turmandreams/pajitaraptor2/images/01.jpg

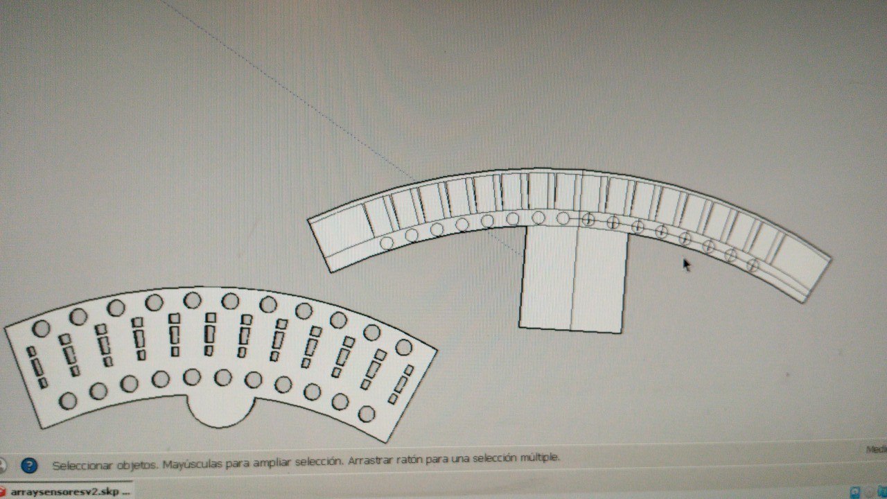
images/01.jpg
