turmandreams/pajitaraptor2/images/02.jpg

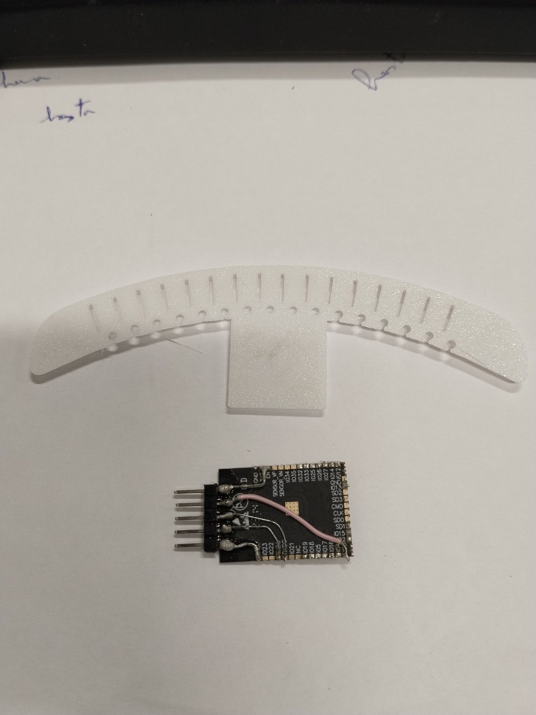
images/02.jpg
