turmandreams/pajitaraptor2/images/03.jpg

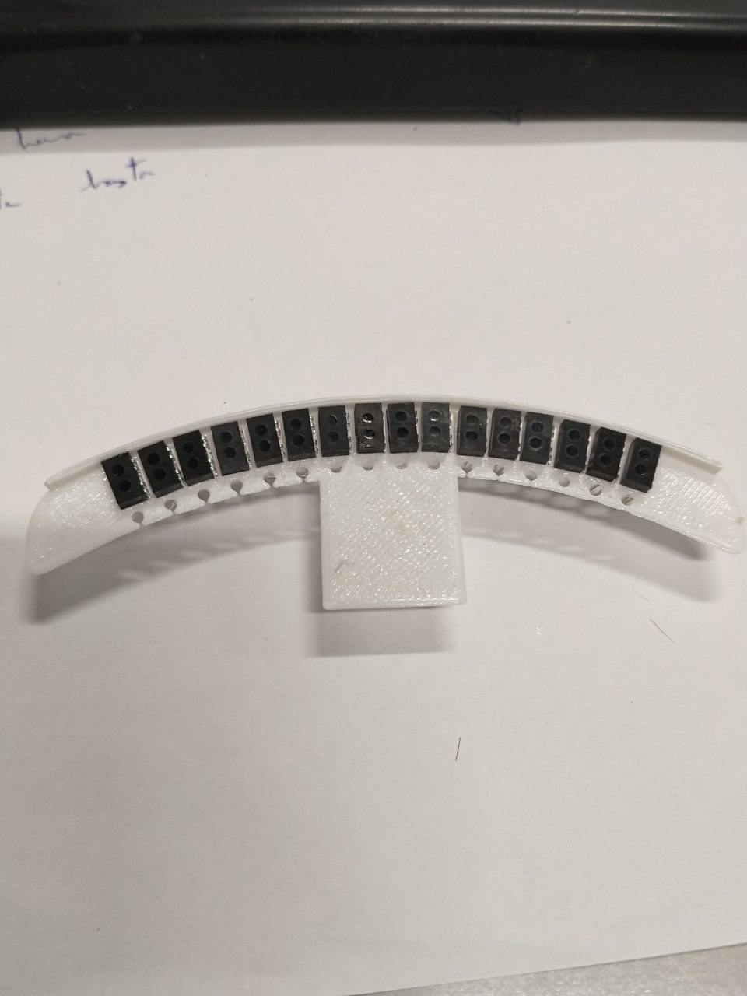
images/03.jpg
