turmandreams/pajitaraptor2/images/04.jpg

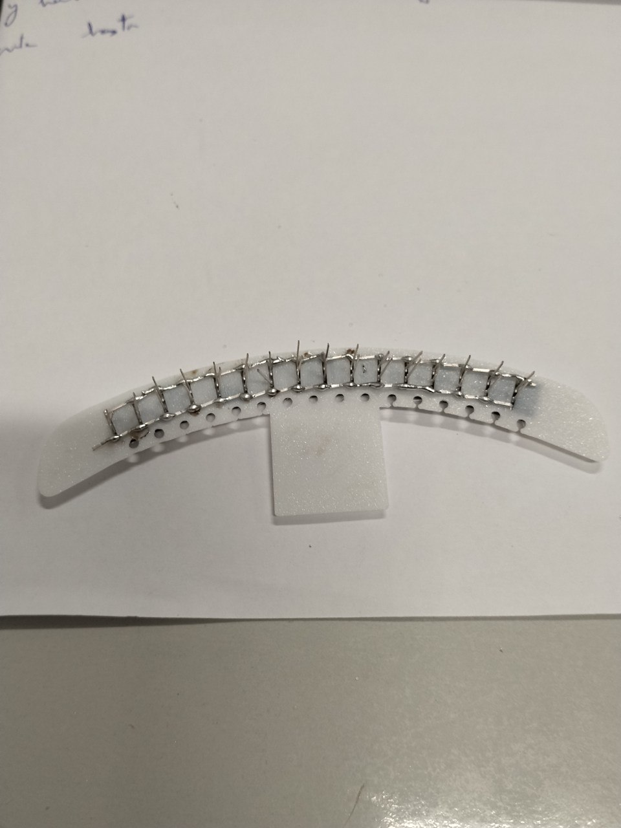
images/04.jpg
