turmandreams/pajitaraptor2/images/05.jpg

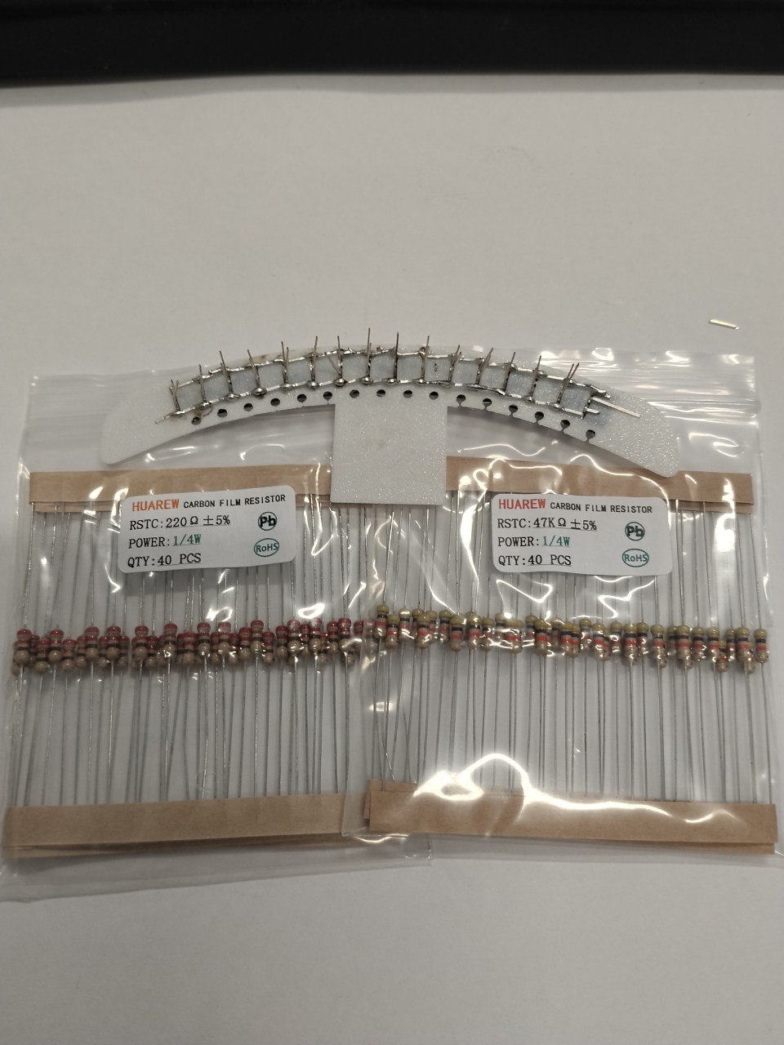
images/05.jpg
