turmandreams/pajitaraptor2/images/07.jpg

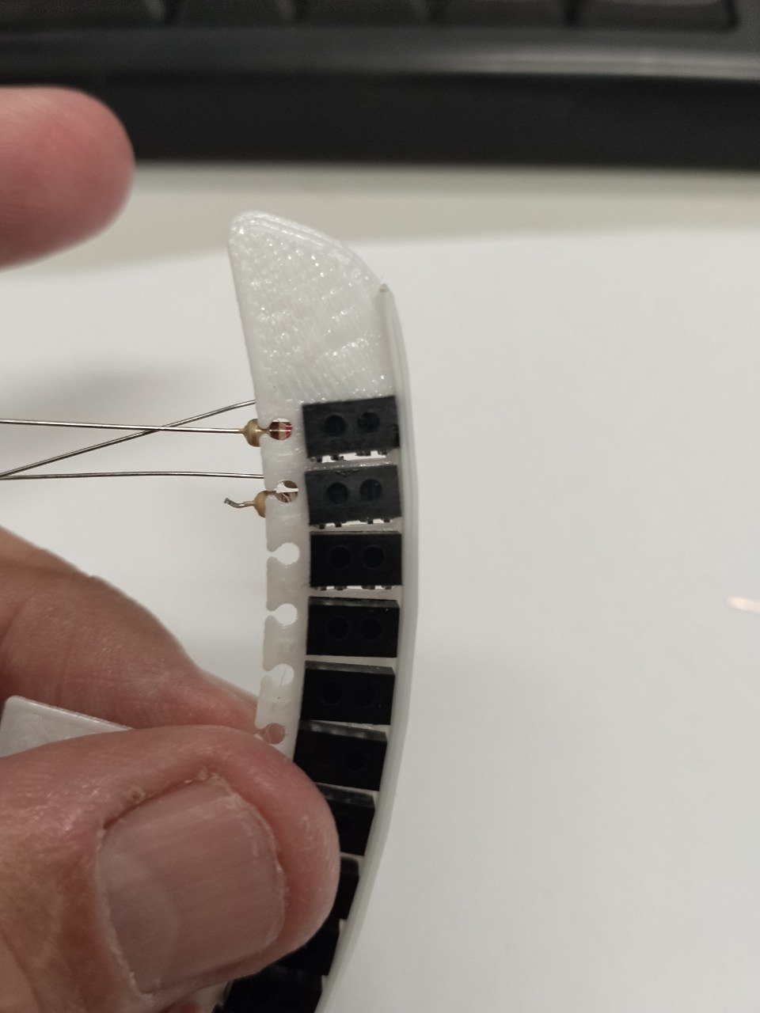
images/07.jpg
