turmandreams/pajitaraptor2/images/08.jpg

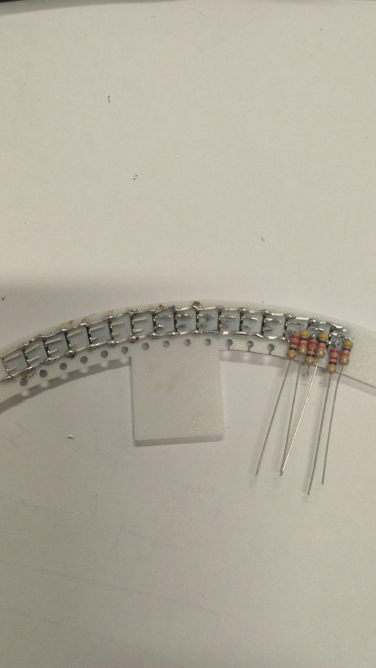
images/08.jpg
