turmandreams/pajitaraptor2/images/09.jpg

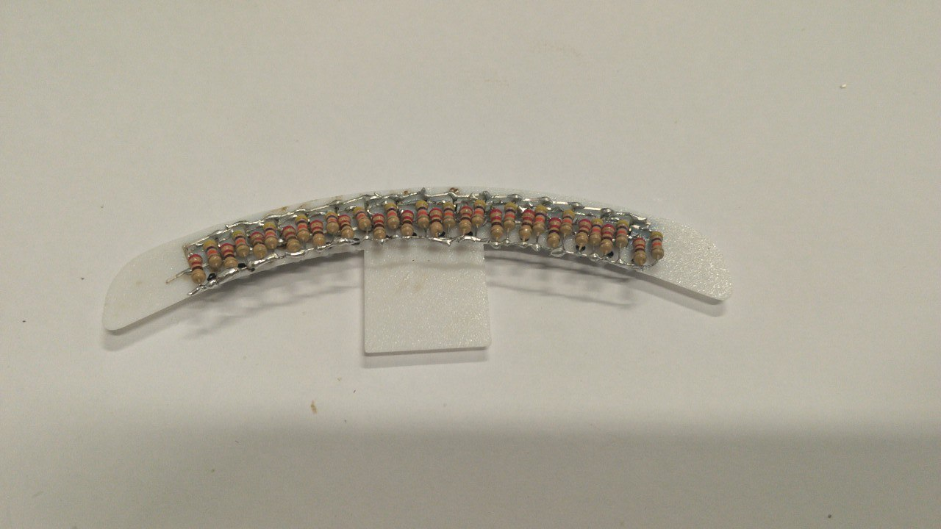
images/09.jpg
