turmandreams/pajitaraptor2/images/10.jpg

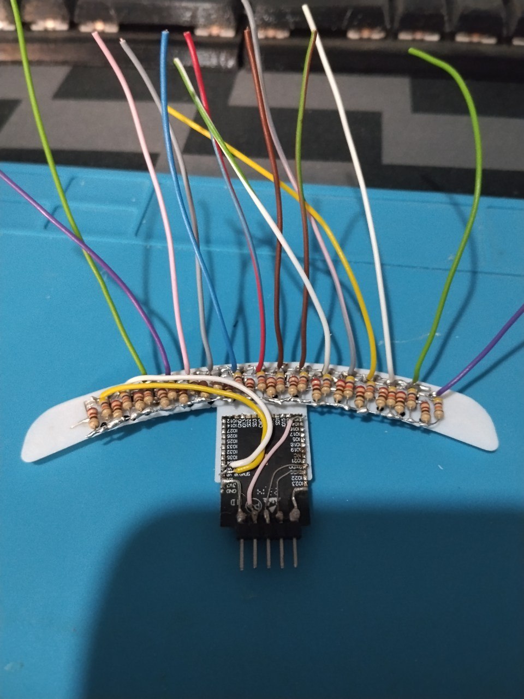
images/10.jpg
