turmandreams/pajitaraptor2/images/11.jpg

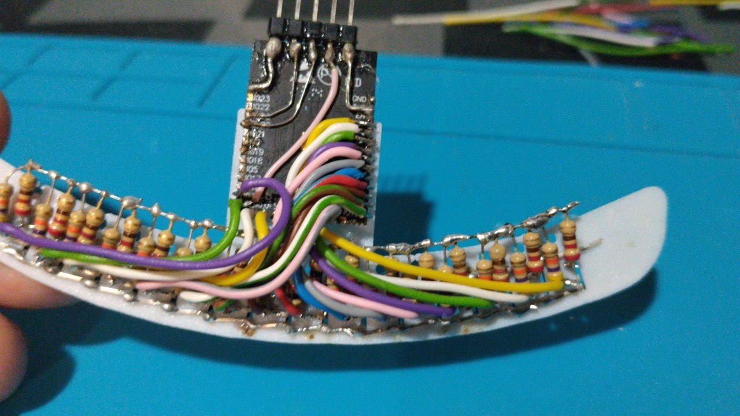
images/11.jpg
