turmandreams/pajitaraptor2/images/12.jpg

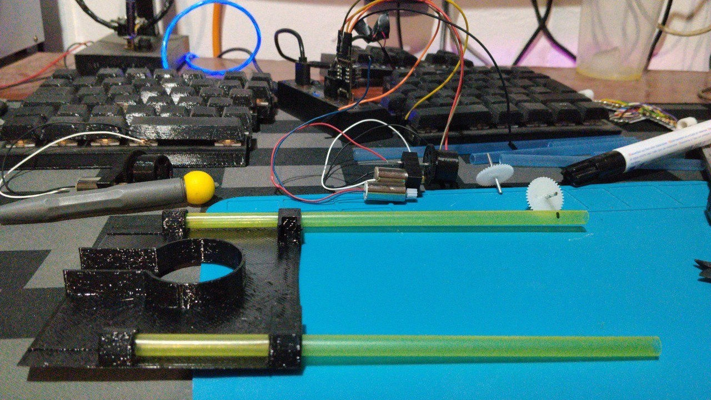
images/12.jpg
