turmandreams/pajitaraptor2/images/13.jpg

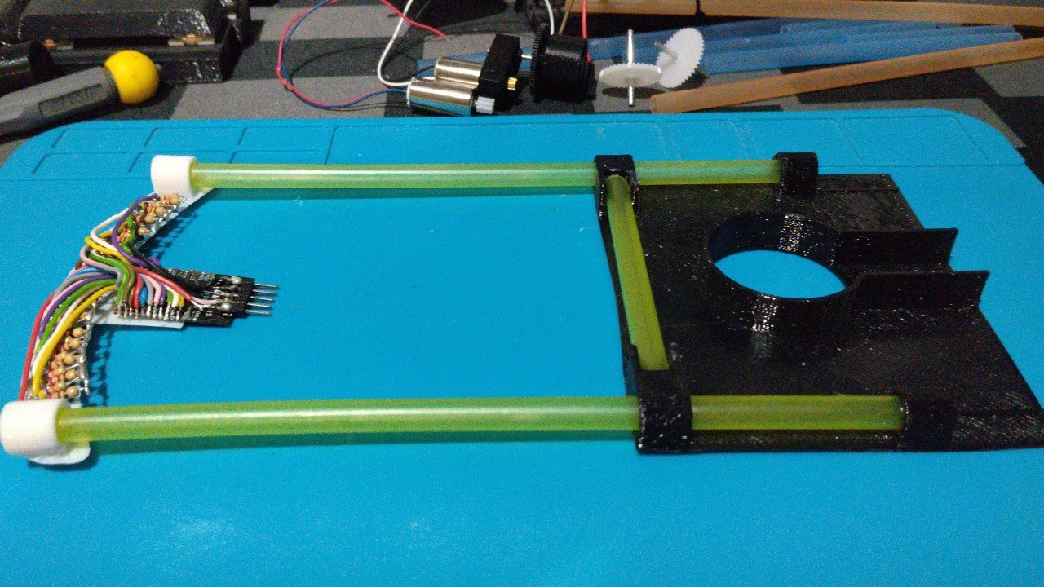
images/13.jpg
