turmandreams/pajitaraptor2/images/14.jpg

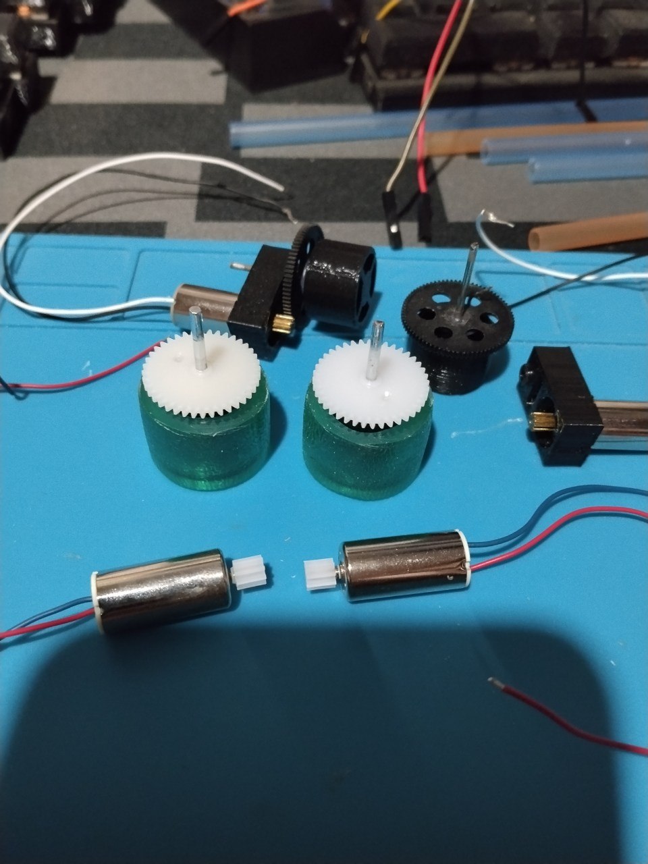
images/14.jpg
