turmandreams/pajitaraptor2/images/15.jpg

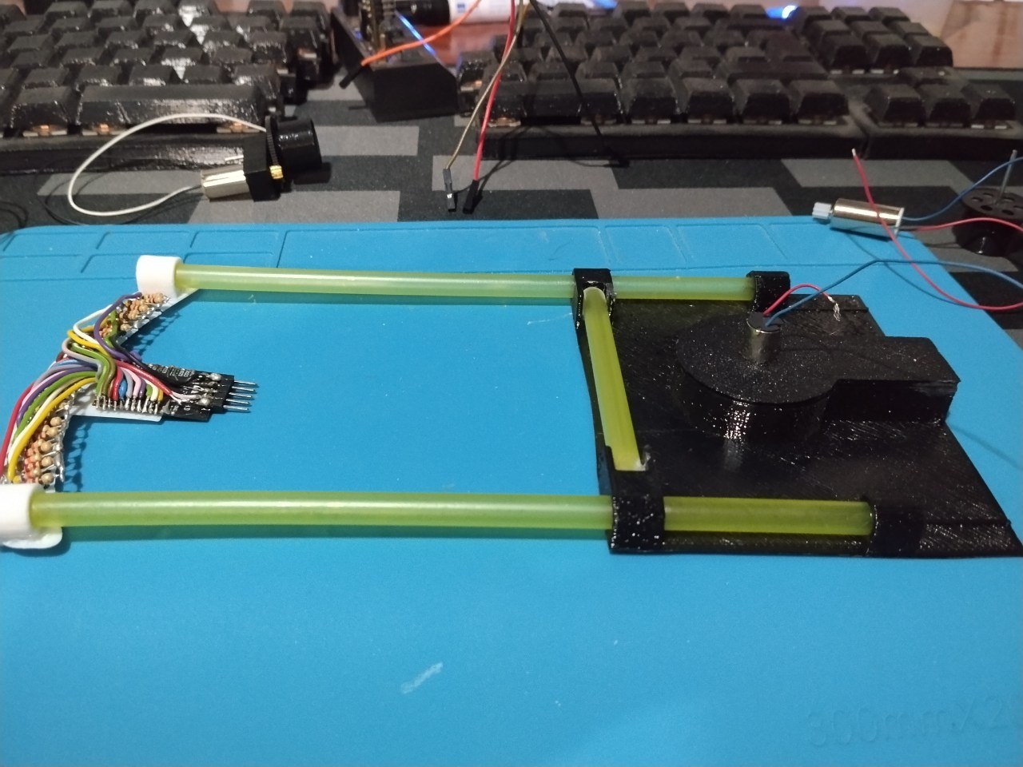
images/15.jpg
