turmandreams/pajitaraptor2/images/16.jpg

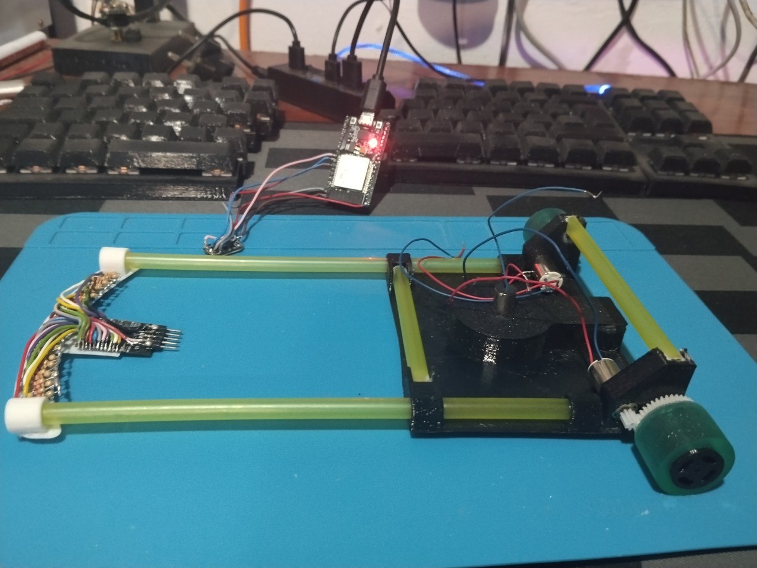
images/16.jpg
