turmandreams/pajitaraptor2/images/17.jpg

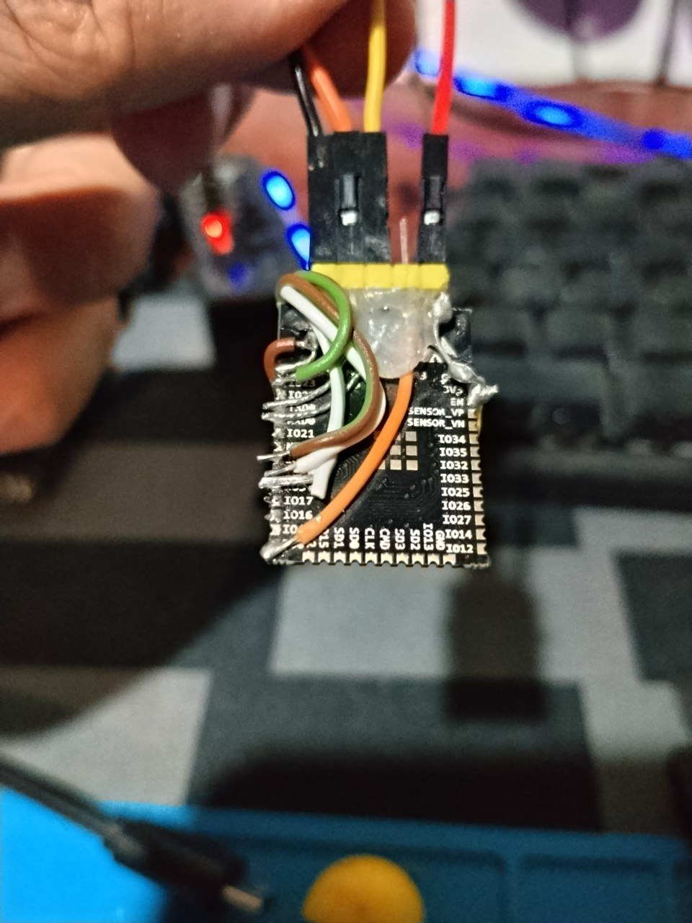
images/17.jpg
