turmandreams/pajitaraptor2/images/18.jpg

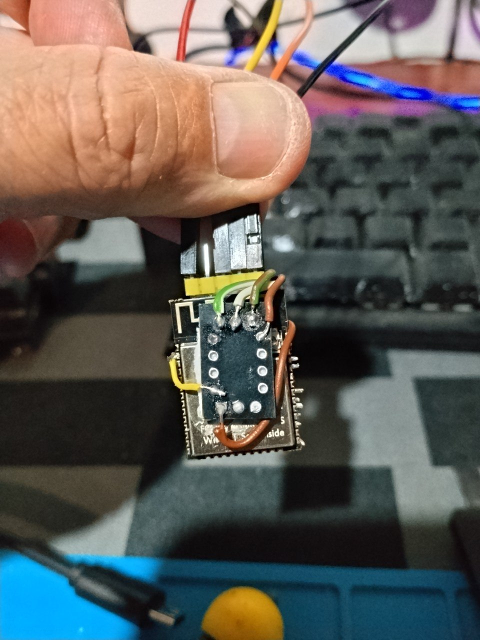
images/18.jpg
