turmandreams/pajitaraptor2/images/19.jpg

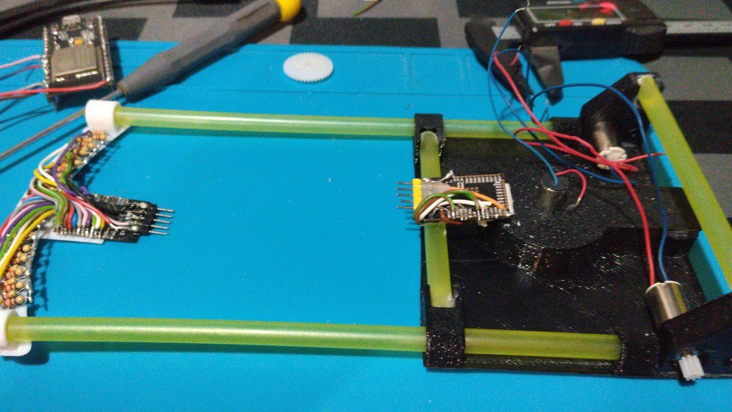
images/19.jpg
