turmandreams/pajitaraptor2/images/20.jpg

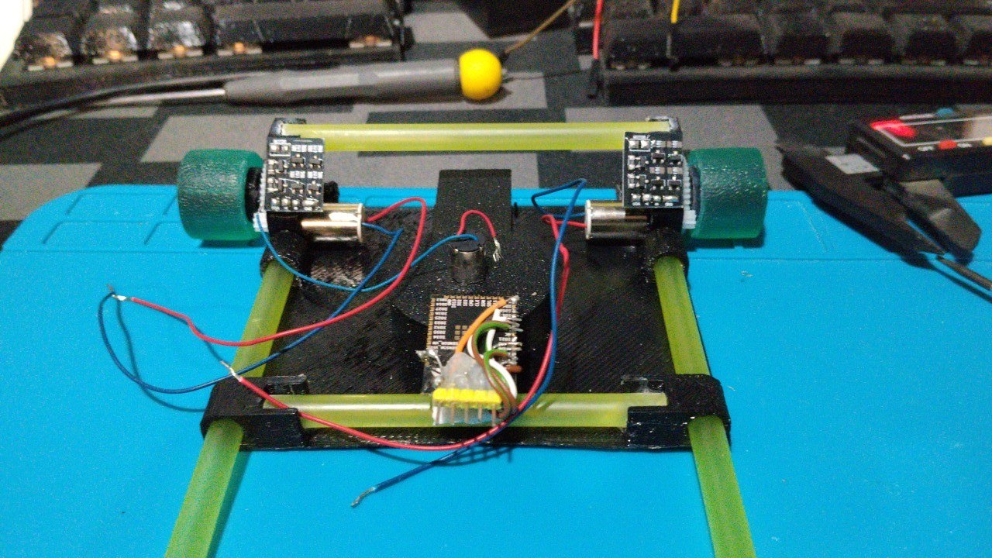
images/20.jpg
