turmandreams/pajitaraptor2/images/21.jpg

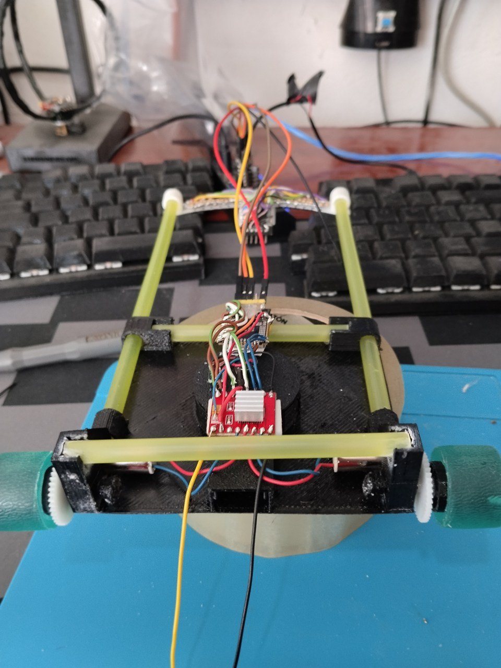
images/21.jpg
