turmandreams/pajitaraptor2/images/22.jpg

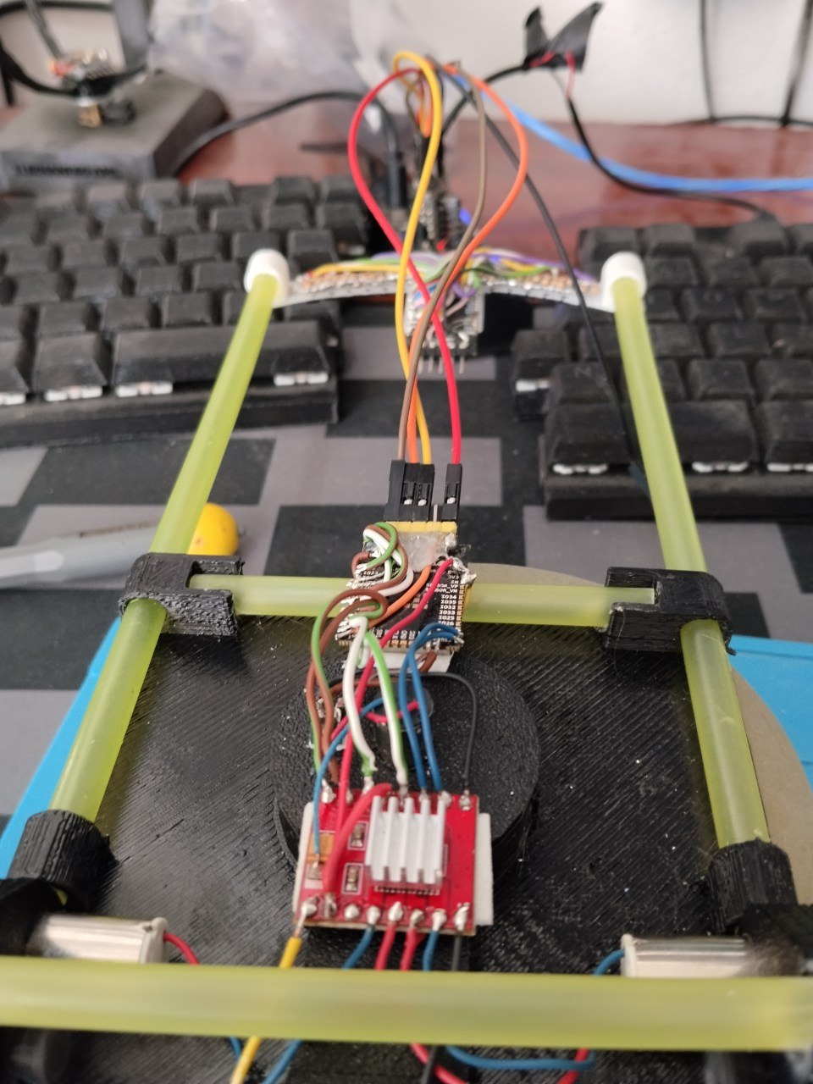
images/22.jpg
