turmandreams/pajitaraptor2/images/23.jpg

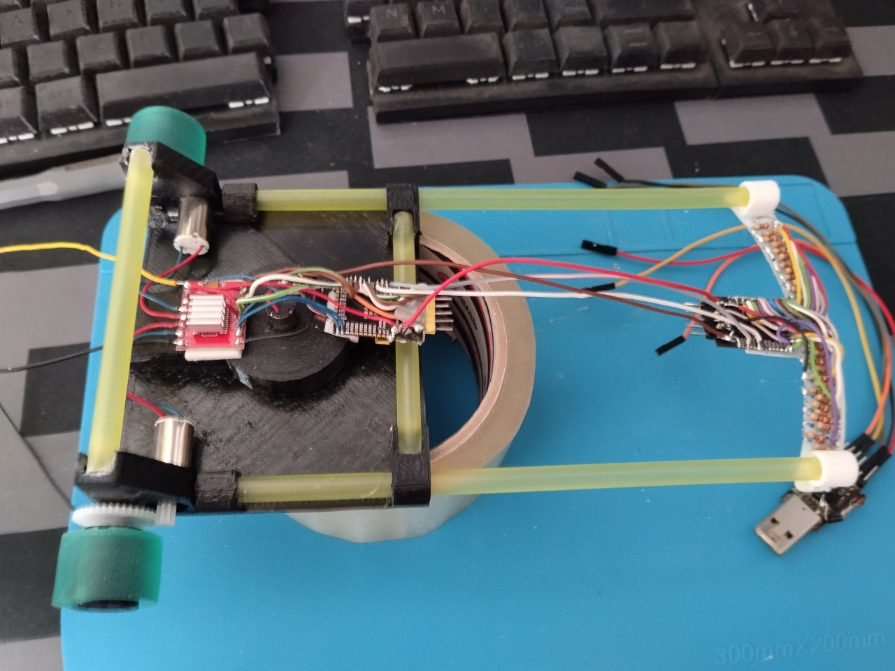
images/23.jpg
