turmandreams/pajitaraptor2/images/24.jpg

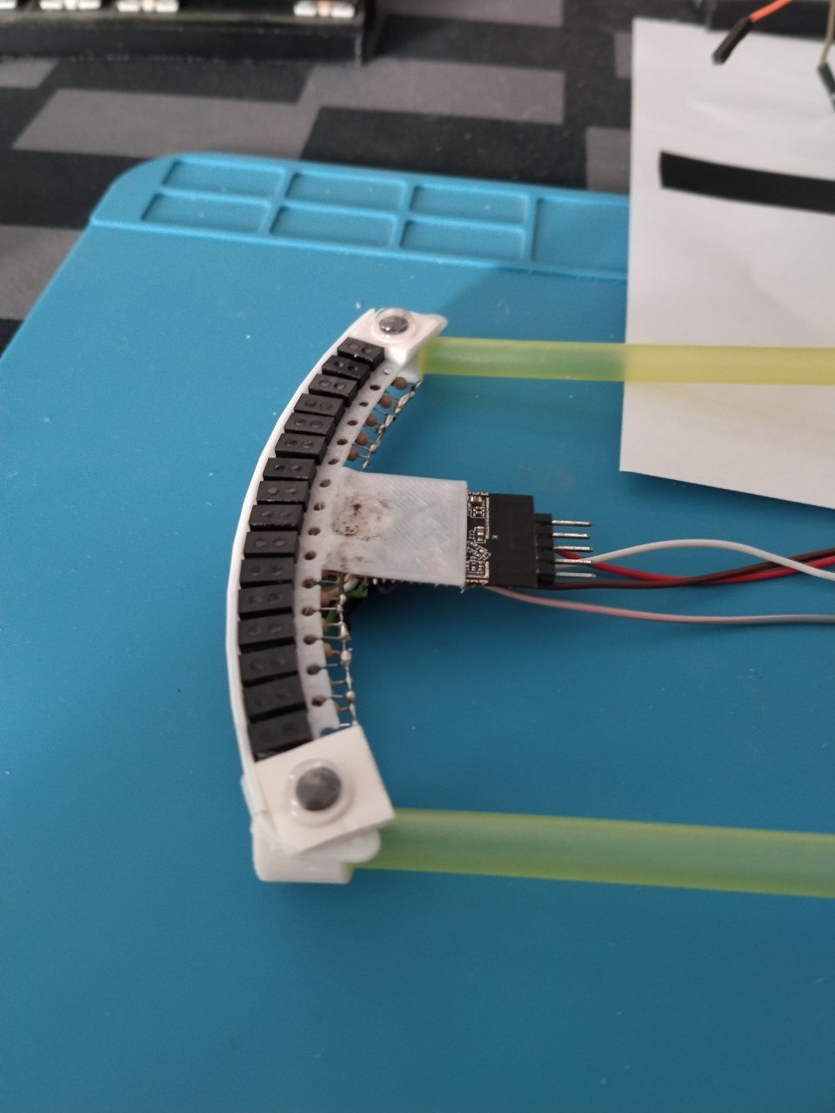
images/24.jpg
