turmandreams/pajitaraptor2/images/25.jpg

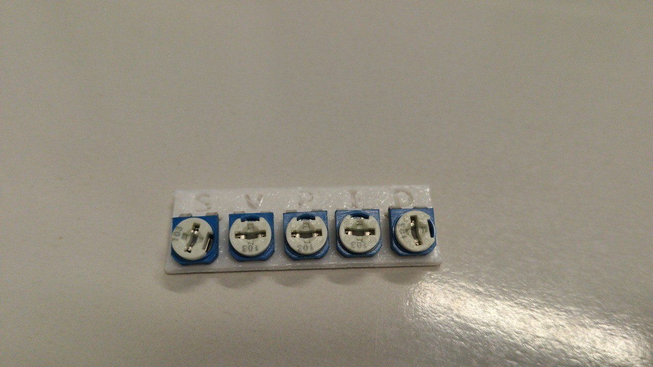
images/25.jpg
