turmandreams/pajitaraptor2/images/26.jpg

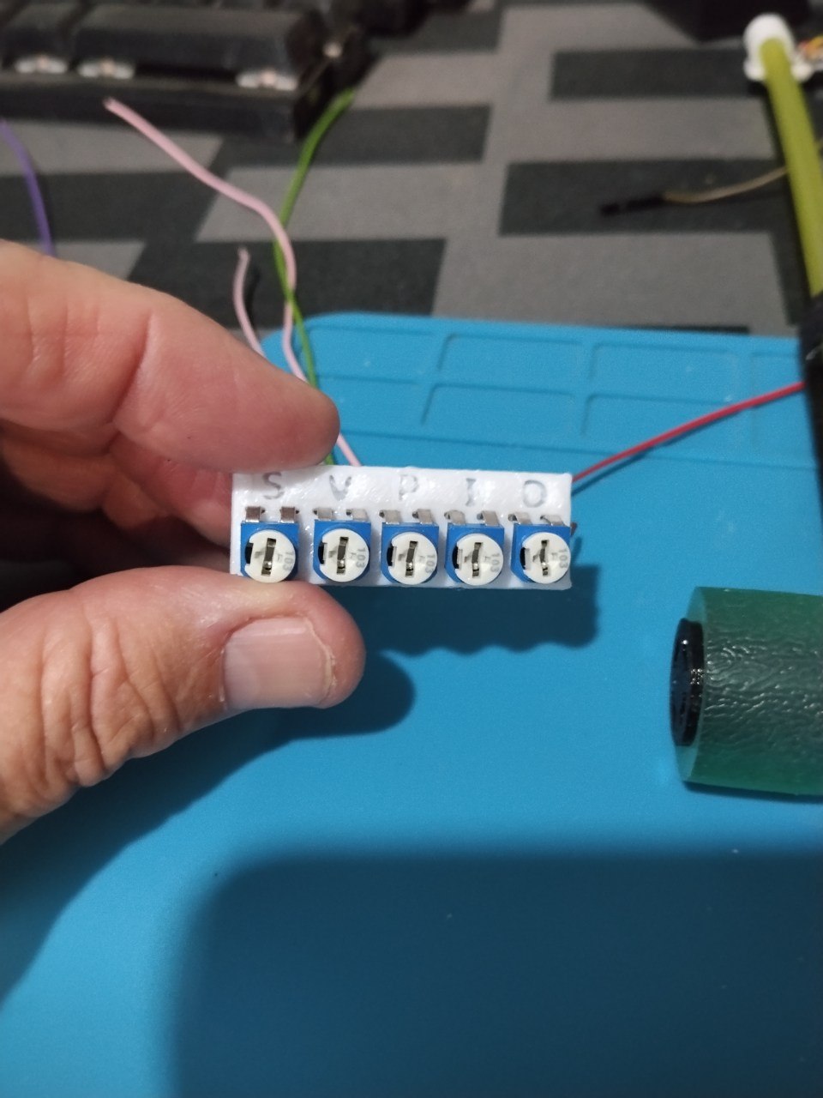
images/26.jpg
