turmandreams/pajitaraptor2/images/27.jpg

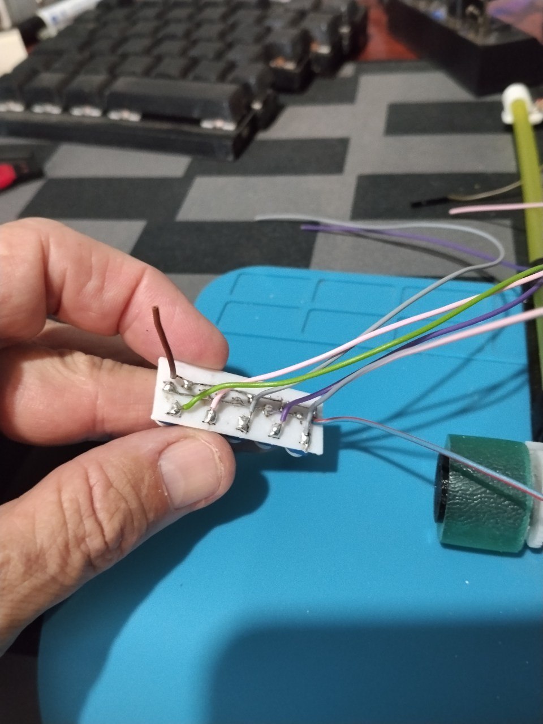
images/27.jpg
