turmandreams/pajitaraptor2/images/28.jpg

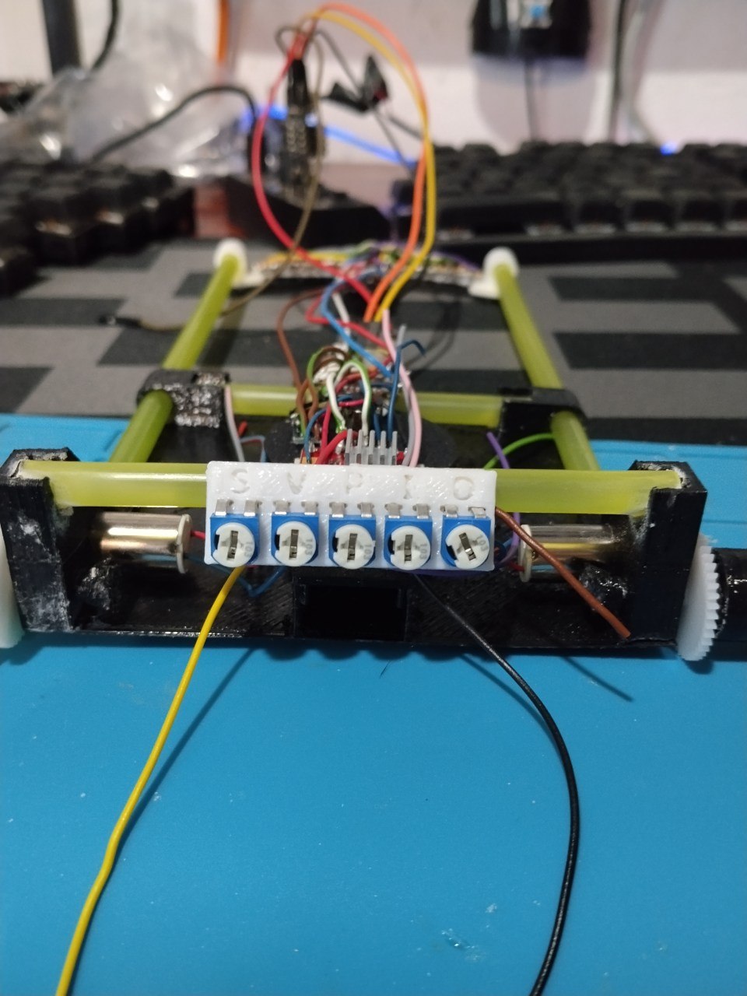
images/28.jpg
