turmandreams/pajitaraptor2/images/29.jpg

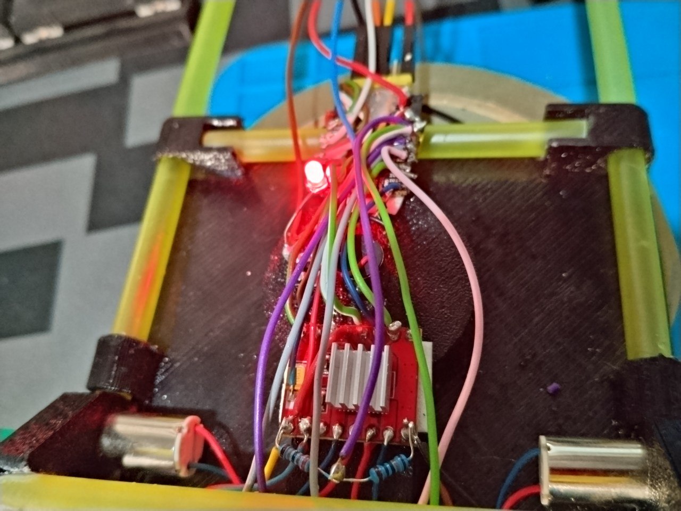
images/29.jpg
