turmandreams/pajitaraptor2/images/30.jpg

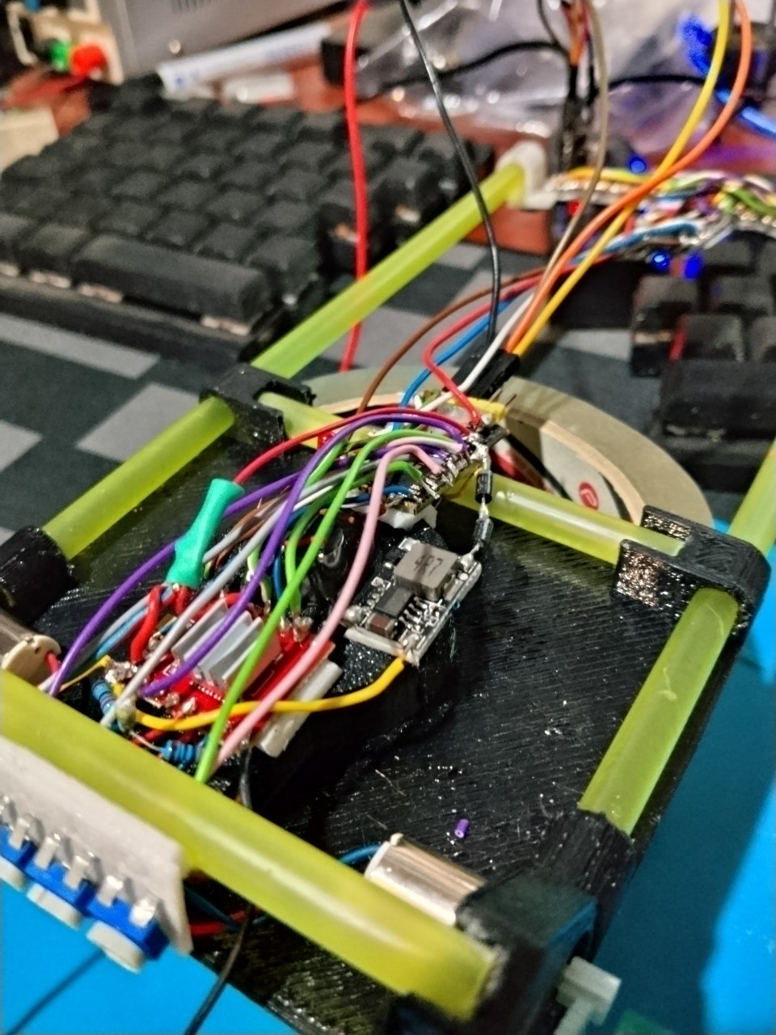
images/30.jpg
