turmandreams/pajitaraptor2/images/31.jpg

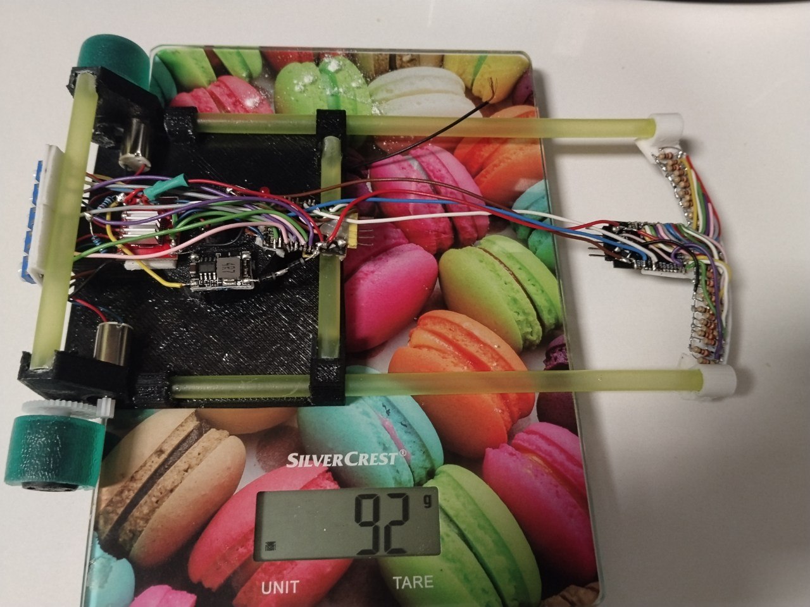
images/31.jpg
