turmandreams/pajitaraptor2/images/33.jpg

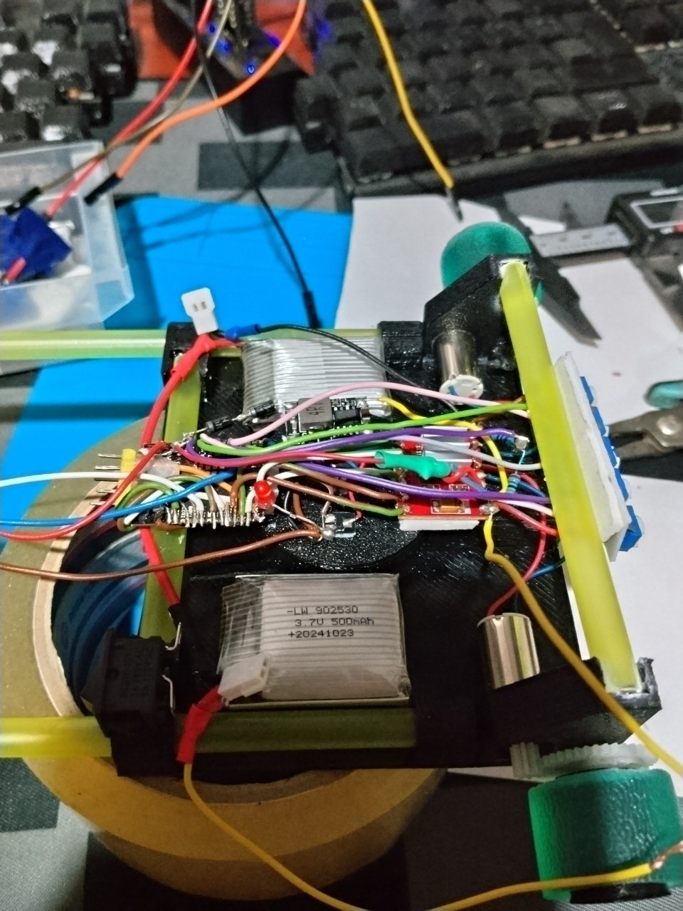
images/33.jpg
