turmandreams/pajitaraptor2/images/34.jpg

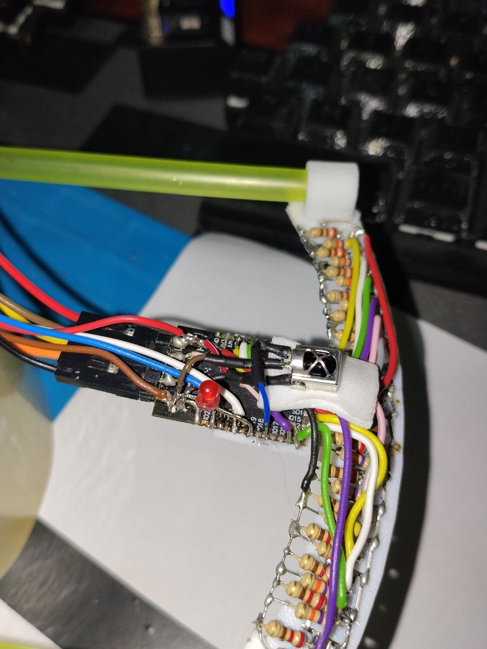
images/34.jpg
